fabriziofiorucci/RetroBench-PSU/pics/Commodore-Power-Supplies.jpg

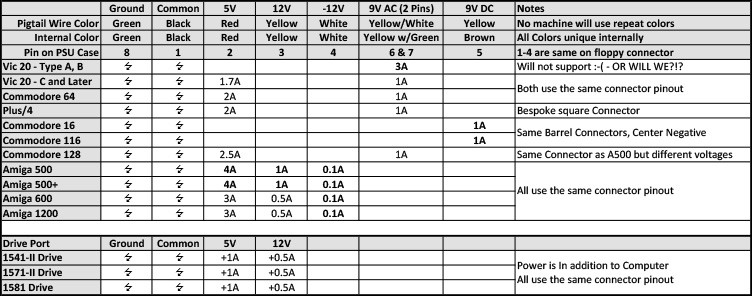
pics/Commodore-Power-Supplies.jpg
