fabriziofiorucci/RetroBench-PSU/pics/psu4.jpg

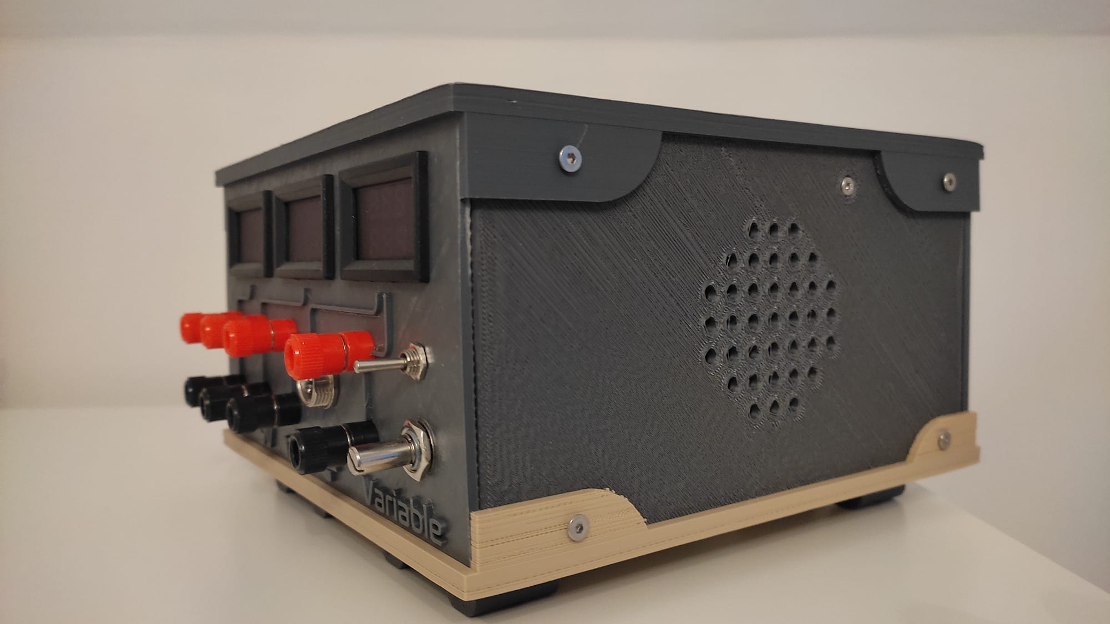
pics/psu4.jpg
