fabriziofiorucci/RetroBench-PSU/pics/psu6.jpg

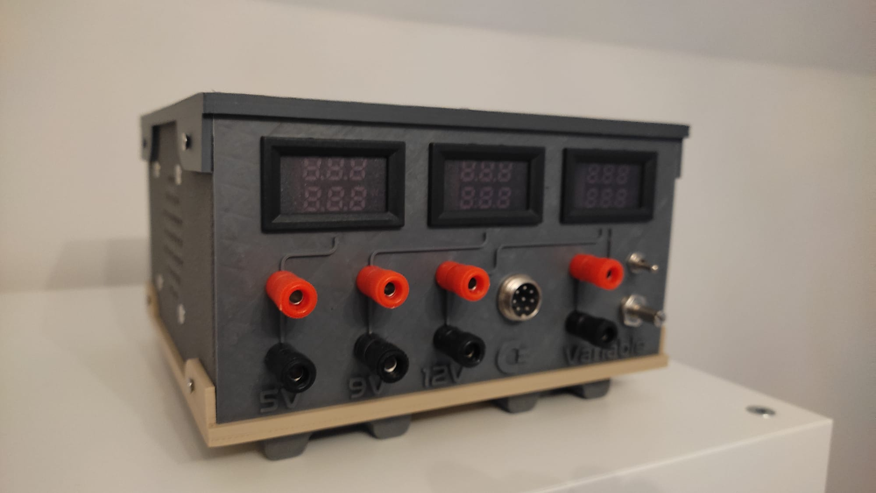
pics/psu6.jpg
